Vateva/STM32ChessClock/include/splash.h

/*
 * splash screen frame data for boot animation
 *
 * generate frames using image2cpp (https://javl.github.io/image2cpp/):

 * canvas size: 128 x 64
 * background color: black
 * Vertical - 1 bit per pixel
 * plain bytes
 * copy the output bytes into the arrays below
 *
 */

#ifndef SPLASH_H
#define SPLASH_H

#include <stdint.h>

// <---- splash configuration ---->

// delay between animation frames in milliseconds
#define SPLASH_FRAME_DELAY_MS    1200

// how long to hold the last frame before proceeding to the clock screen (ms)
#define SPLASH_HOLD_LAST_FRAME_MS  2000

// number of animation frames (update this to match your frame count)
#define SPLASH_FRAME_COUNT  4

// <---- frame data ---->

static const uint8_t splash_frame_0[1024] = {
0x00, 0x00, 0x00, 0x00, 0x00, 0x00, 0x00, 0x00, 0x00, 0x00, 0x00, 0x00, 0x00, 0x00, 0x00, 0x00, 
0x00, 0x00, 0x00, 0x00, 0x00, 0x00, 0x00, 0x00, 0x00, 0x00, 0x00, 0x00, 0x00, 0x00, 0x00, 0x00, 
0x00, 0x00, 0x00, 0x00, 0x00, 0x00, 0x00, 0x00, 0x00, 0x00, 0x00, 0x00, 0x00, 0x00, 0x00, 0x00, 
0x00, 0x00, 0x00, 0x00, 0x00, 0x00, 0x00, 0x00, 0x00, 0x00, 0x00, 0x00, 0x00, 0x00, 0x00, 0x00, 
0x00, 0x00, 0x00, 0x00, 0x00, 0x00, 0x00, 0x00, 0x00, 0x00, 0x00, 0x00, 0x00, 0x00, 0x00, 0x00, 
0x00, 0x00, 0x00, 0x00, 0x00, 0x00, 0x00, 0x00, 0x00, 0x00, 0x00, 0x00, 0x00, 0x00, 0x00, 0x00, 
0x00, 0x00, 0x00, 0x00, 0x00, 0x00, 0x00, 0x00, 0x00, 0x00, 0x00, 0x00, 0x00, 0x00, 0x00, 0x00, 
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
 };

// <---- frame table ---->

// array of pointers to each frame
static const uint8_t* const splash_frames[SPLASH_FRAME_COUNT] = {
    splash_frame_0,
    splash_frame_1,
    splash_frame_2,
    splash_frame_3

};

#endif  // SPLASH_H
