Vateva/STM32ChessClock/include/display.h

/*
 * display driver interface for sh1106 oled displays
 * provides functions for initializing and drawing on the displays
 */

#ifndef DISPLAY_H
#define DISPLAY_H

#include <stdint.h>

#include "config.h"
#include "stm32f1xx_hal.h"

// <---- display initialization ---->

/**
 * initialize sh1106 display
 * must be called before any other display functions
 *
 * @param i2c_handle pointer to initialized i2c handle
 */
void display_init(I2C_HandleTypeDef* i2c_handle);

// <---- display control ---->

/**
 * clear entire display
 * sets all pixels to off
 *
 * @param i2c_handle pointer to i2c handle for this display
 */
void display_clear(I2C_HandleTypeDef* i2c_handle);

/**
 * set cursor position for next draw operation
 *
 * @param i2c_handle pointer to i2c handle for this display
 * @param x_position horizontal position in pixels (0-127)
 * @param page vertical page (0-7, each page is 8 pixels tall)
 */
void display_set_position(I2C_HandleTypeDef* i2c_handle, uint8_t x_position, uint8_t page);

// <---- bitmap drawing ---->

/**
 * draw a full-screen 128x64 monochrome bitmap
 * data format: 8 pages of 128 bytes each (1024 bytes total)
 * each byte is 8 vertical pixels, lsb = top pixel
 * matches image2cpp "vertical" draw mode output
 *
 * @param i2c_handle pointer to i2c handle for this display
 * @param bitmap pointer to 1024-byte bitmap array
 */
void display_draw_bitmap(I2C_HandleTypeDef* i2c_handle, const uint8_t* bitmap);

// <---- text drawing ---->

/**
 * draw single character at specified position
 * uses 5x7 pixel font
 * used for all text(menu+mode+"Ready!")
 *
 * @param i2c_handle pointer to i2c handle for this display
 * @param x_position horizontal position in pixels (0-127)
 * @param page vertical page (0-7)
 * @param character character to draw (ascii 32-122 supported: space through z)
 */
void display_draw_character(I2C_HandleTypeDef* i2c_handle, uint8_t x_position, uint8_t page, char character);

/**
 * draw string at specified position
 * automatically advances cursor for each character
 * uses 5x7 pixel font
 *
 * @param i2c_handle pointer to i2c handle for this display
 * @param x_position starting horizontal position in pixels (0-127)
 * @param page vertical page (0-7)
 * @param text null-terminated string to draw
 */
void display_draw_string(I2C_HandleTypeDef* i2c_handle, uint8_t x_position, uint8_t page, const char* text);

/**
 * draw large character at specified position
 * uses 16x24 pixel font, spans 3 pages vertically
 * supports digits 0-9, colon, and period
 * used for clock
 *
 * @param i2c_handle pointer to i2c handle for this display
 * @param x_position horizontal position in pixels (0-127)
 * @param start_page starting vertical page (0-5, since it spans 3 pages)
 * @param character character to draw
 */
void display_draw_large_character(I2C_HandleTypeDef* i2c_handle,
                                  uint8_t x_position,
                                  uint8_t start_page,
                                  char character);

/**
 * draw medium character at specified position
 * uses 8x16 pixel font, spans 2 pages vertically
 * supports digits 0-9 and 's'
 * used for bonus time
 *
 * @param i2c_handle pointer to i2c handle for this display
 * @param x_position horizontal position in pixels (0-127)
 * @param start_page starting vertical page (0-6, since it spans 2 pages)
 * @param character character to draw
 */
void display_draw_medium_character(I2C_HandleTypeDef* i2c_handle,
                                   uint8_t x_position,
                                   uint8_t start_page,
                                   char character);

// <---- clock screen elements ---->

/**
 * draw mode header
 * shows mode name on top left and bonus time on top right
 *
 * @param i2c_handle pointer to i2c handle for this display
 * @param mode time control mode (for header label)
 * @param bonus_time_milliseconds bonus time to display (seconds value in top right)
 */

void display_draw_header(I2C_HandleTypeDef* i2c_handle, time_control_mode_t mode, uint32_t bonus_time_milliseconds);

/**
 * draw time as large centered clock
 * always displays HH:MM:SS format
 *
 * @param i2c_handle pointer to i2c handle for this display
 * @param time_milliseconds main time to display in milliseconds
 */
void display_draw_clock(I2C_HandleTypeDef* i2c_handle, uint32_t time_milliseconds);

/**
 * update only the bonus time digits in the header
 * partial redraw for countdown modes (delay, limited, byo-yomi)
 * avoids clearing and redrawing the mode name
 *
 * @param i2c_handle pointer to i2c handle for this display
 * @param bonus_time_milliseconds current bonus time in milliseconds
 */
void display_update_header_bonus(I2C_HandleTypeDef* i2c_handle, uint32_t bonus_time_milliseconds);

/**
 * draw ready footer
 * draws "Ready!" under a players clock when ready
 *
 * @param i2c_handle pointer to i2c handle for this display
 * @param is_ready if TRUE, displays "Ready!" below the clock
 */
void display_draw_footer(I2C_HandleTypeDef* i2c_handle, uint8_t is_ready);

/**
 * draw full clock screen
 * calls display_draw_header and display_draw_clock
 * header + clock + footer
 *
 * @param i2c_handle pointer to i2c handle for this display
 * @param time_milliseconds main time to display in milliseconds
 * @param mode time control mode (for header label)
 * @param bonus_time_milliseconds bonus time to display (seconds value in top right)
 * @param is_ready if TRUE, displays "Ready!" below the clock
 */
void display_draw_clock_screen(I2C_HandleTypeDef* i2c_handle,
                               uint32_t time_milliseconds,
                               time_control_mode_t mode,
                               uint32_t bonus_time_millisecond,
                               uint8_t is_ready);

// <---- splash screen ---->

/**
 * play splash screen animation on both displays
 * shows each frame from splash.h with configured delays
 *
 * @param i2c1 pointer to i2c handle for player 1 display
 * @param i2c2 pointer to i2c handle for player 2 display
 */
void display_show_splash(I2C_HandleTypeDef* i2c1, I2C_HandleTypeDef* i2c2);

// <---- low-level communication ---->

/**
 * send command to sh1106 display
 * internal function, typically not called directly
 *
 * @param i2c_handle pointer to i2c handle for this display
 * @param command command byte to send
 */
void display_send_command(I2C_HandleTypeDef* i2c_handle, uint8_t command);

#endif  // DISPLAY_H
